pvanroy/Tektronix-CCD-Cooler/Pictures/IMG_20220201_145929.jpg

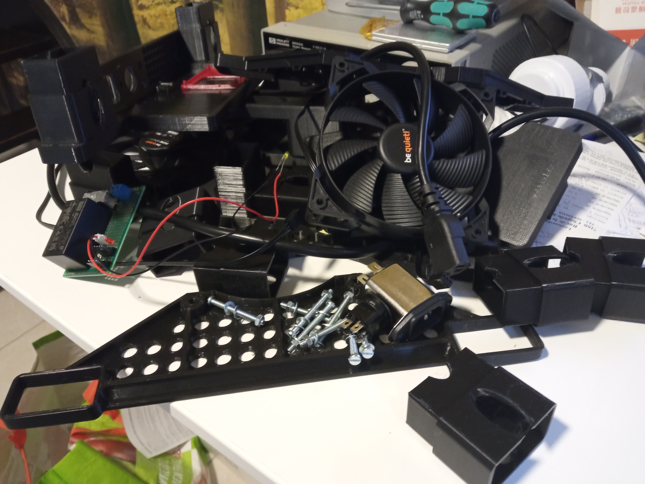
Pictures/IMG_20220201_145929.jpg
