pvanroy/Tektronix-CCD-Cooler/Pictures/IMG_20220201_165314.jpg

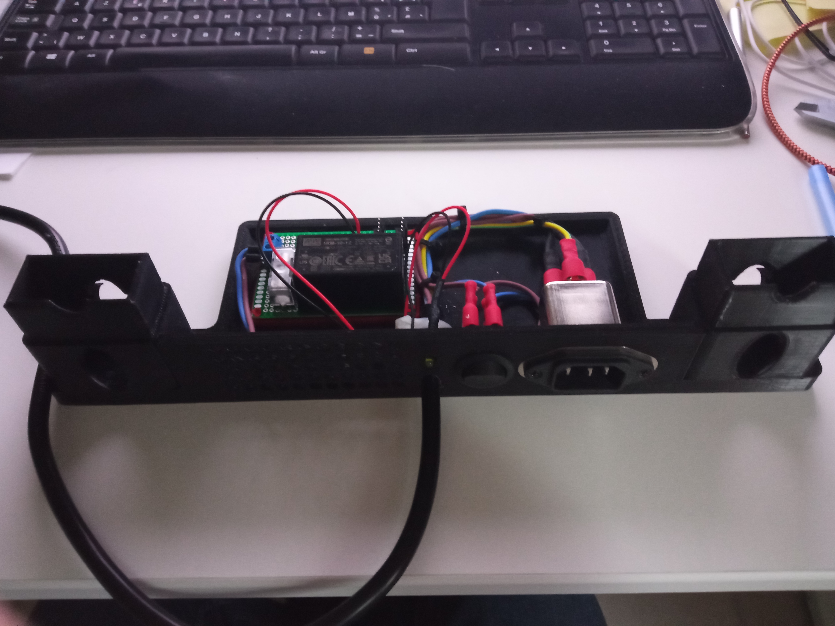
Pictures/IMG_20220201_165314.jpg
