pvanroy/Tektronix-CCD-Cooler/Pictures/IMG_20220201_165510.jpg

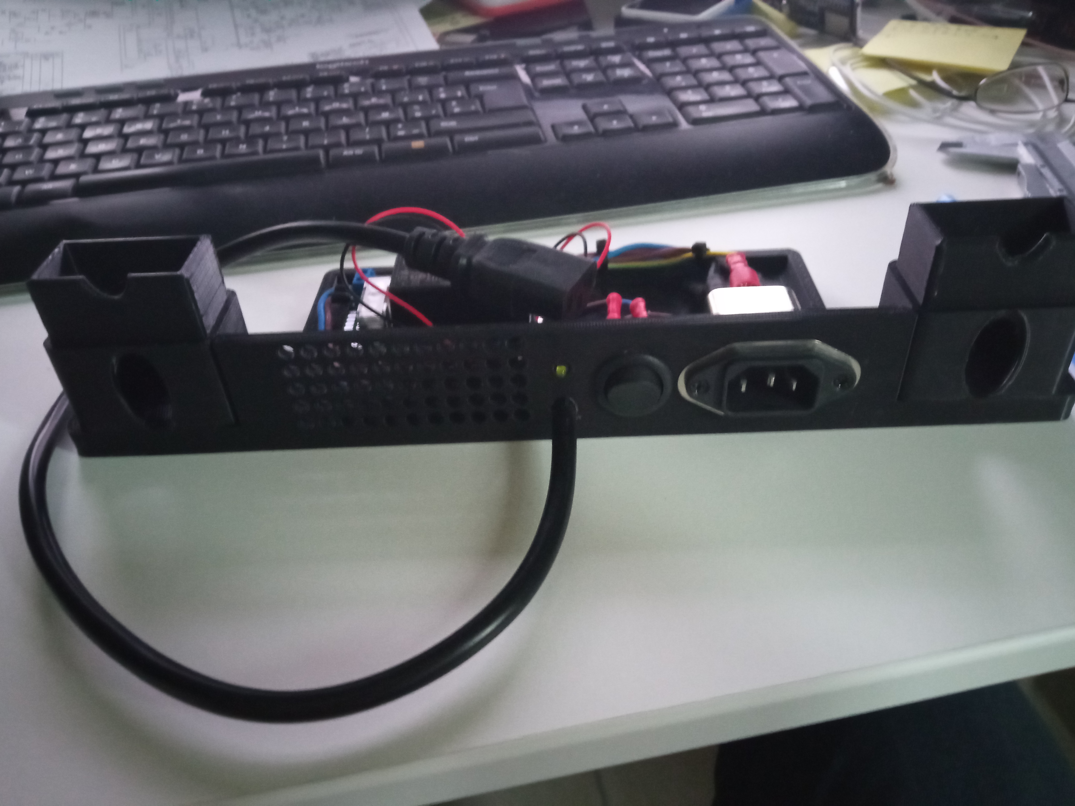
Pictures/IMG_20220201_165510.jpg
