pvanroy/Tektronix-CCD-Cooler/Pictures/IMG_20220201_170256.jpg

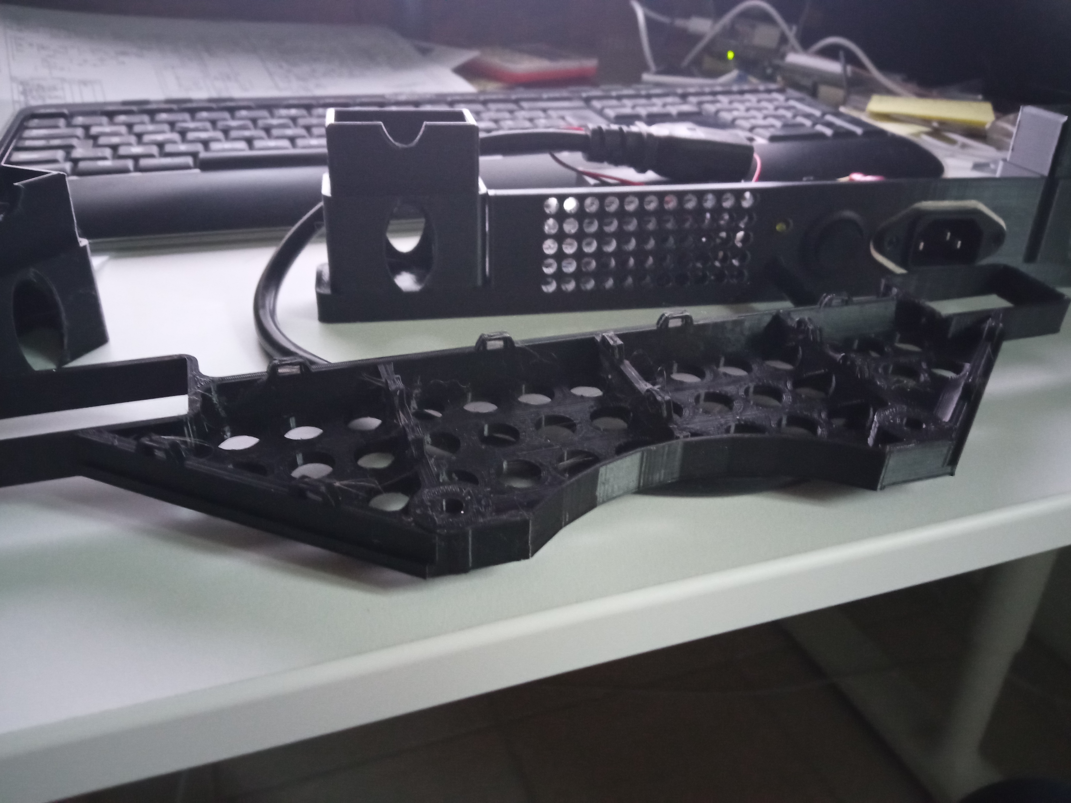
Pictures/IMG_20220201_170256.jpg
