pvanroy/Tektronix-CCD-Cooler/Pictures/IMG_20220201_171011.jpg

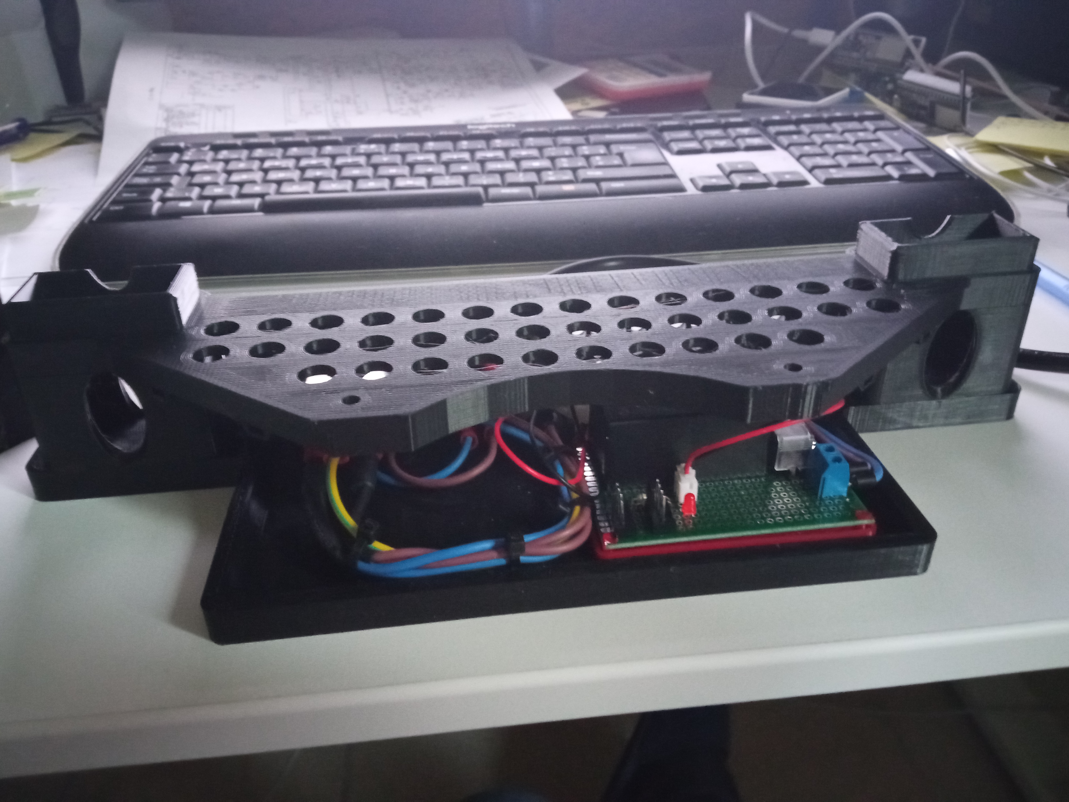
Pictures/IMG_20220201_171011.jpg
