pvanroy/Tektronix-CCD-Cooler/Pictures/IMG_20220201_171432.jpg

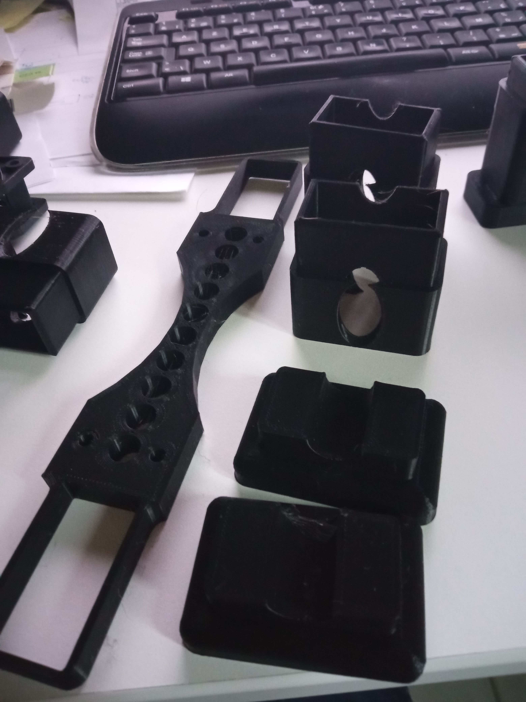
Pictures/IMG_20220201_171432.jpg
