pvanroy/Tektronix-CCD-Cooler/Pictures/IMG_20220202_084107.jpg

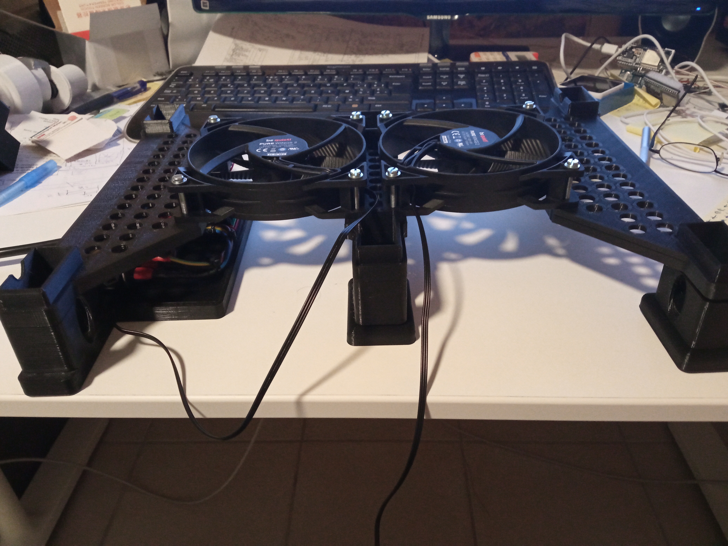
Pictures/IMG_20220202_084107.jpg
