pvanroy/Tektronix-CCD-Cooler/Pictures/IMG_20220202_085803.jpg

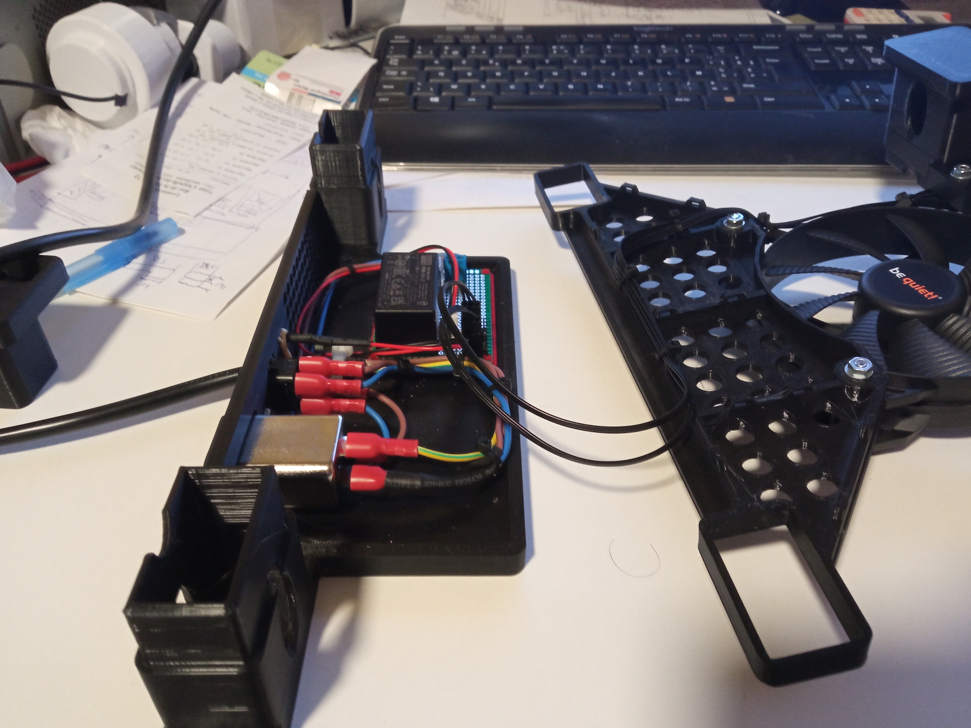
Pictures/IMG_20220202_085803.jpg
