pvanroy/Tektronix-CCD-Cooler/Pictures/IMG_20220202_085853.jpg

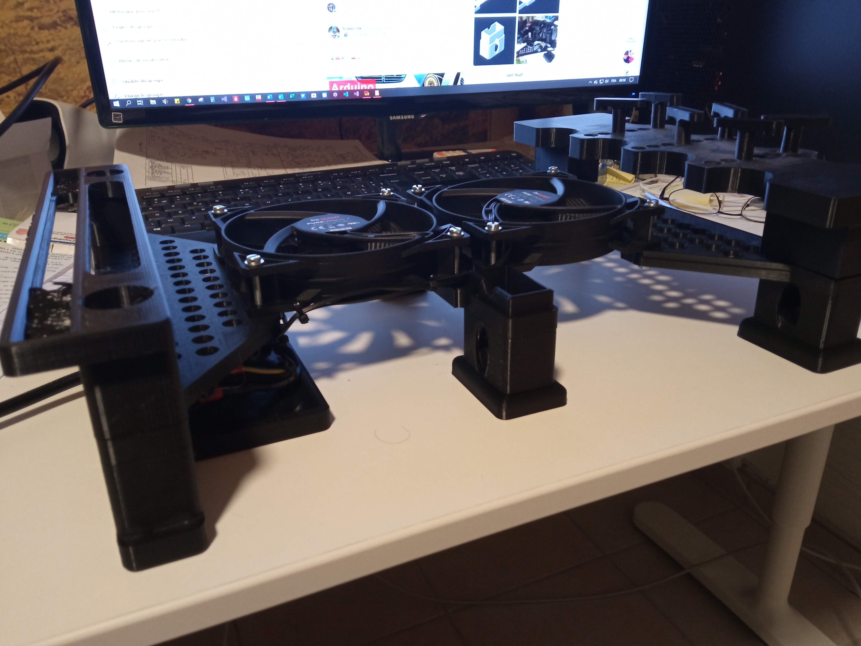
Pictures/IMG_20220202_085853.jpg
