pvanroy/Tektronix-CCD-Cooler/Pictures/IMG_20220202_085902.jpg

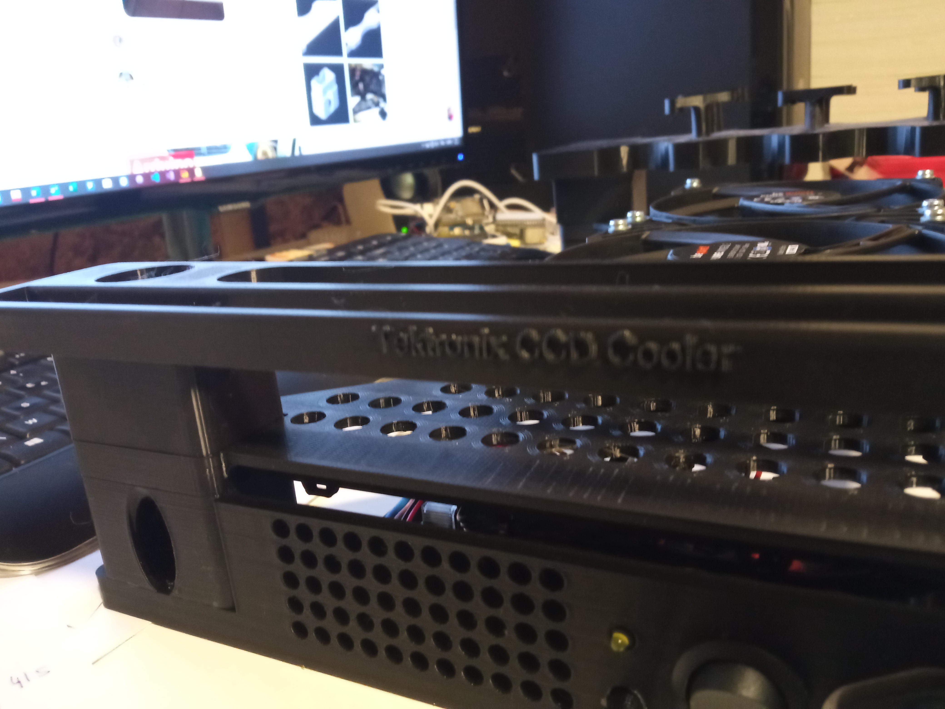
Pictures/IMG_20220202_085902.jpg
