pvanroy/Tektronix-CCD-Cooler/Pictures/IMG_20220202_090543.jpg

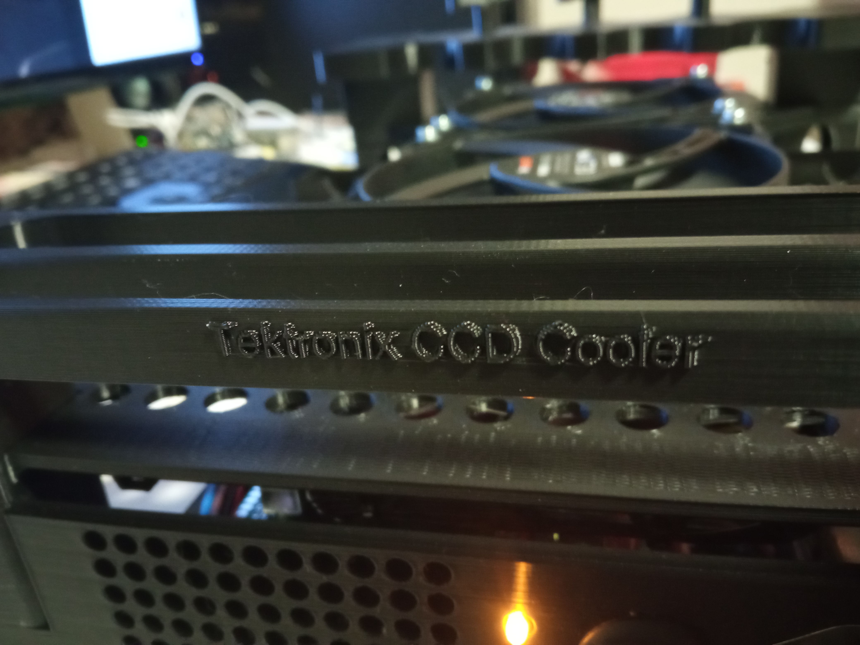
Pictures/IMG_20220202_090543.jpg
