pvanroy/Tektronix-CCD-Cooler/Pictures/IMG_20220208_113421.jpg

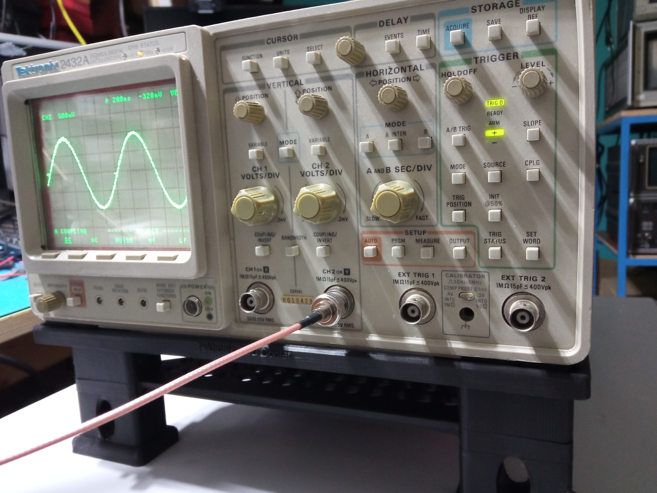
Pictures/IMG_20220208_113421.jpg
