pvanroy/Tektronix-CCD-Cooler/Pictures/IMG_20220208_113443.jpg

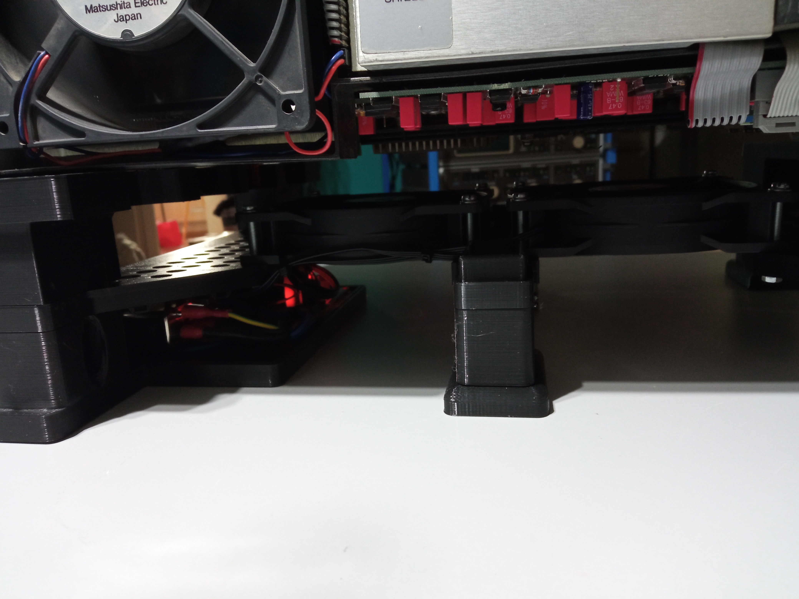
Pictures/IMG_20220208_113443.jpg
