pvanroy/Tektronix-CCD-Cooler/Pictures/IMG_20220208_113453.jpg

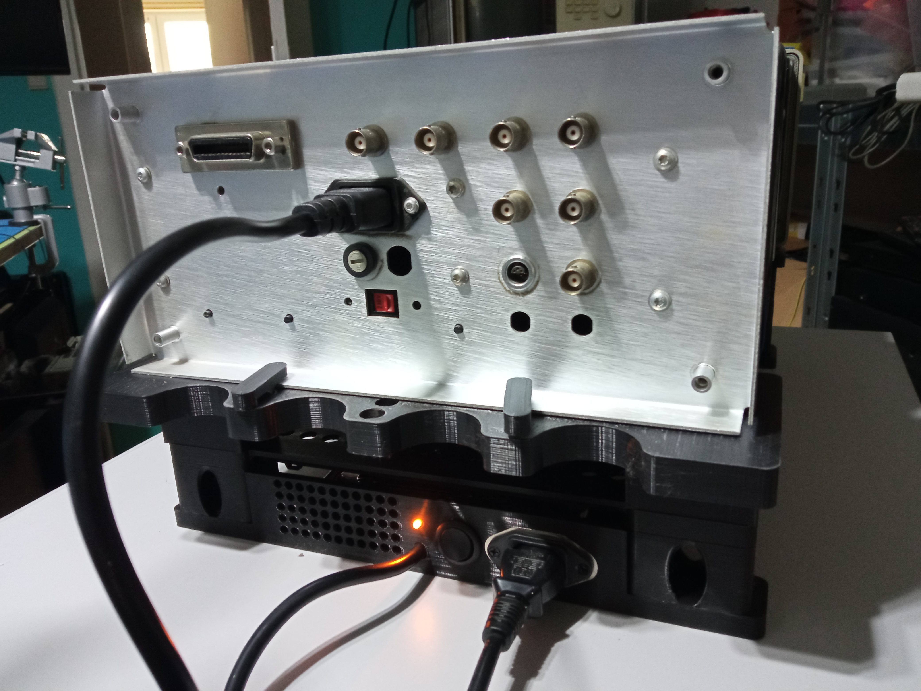
Pictures/IMG_20220208_113453.jpg
