pvanroy/Tektronix-CCD-Cooler/Pictures/IMG_20220208_122140.jpg

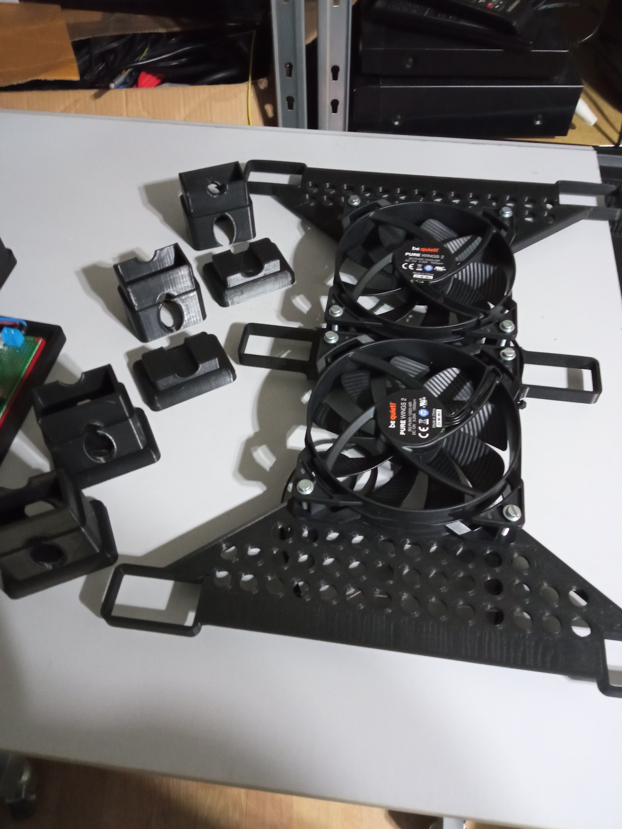
Pictures/IMG_20220208_122140.jpg
