pvanroy/Tektronix-CCD-Cooler/Pictures/IMG_20220208_122149.jpg

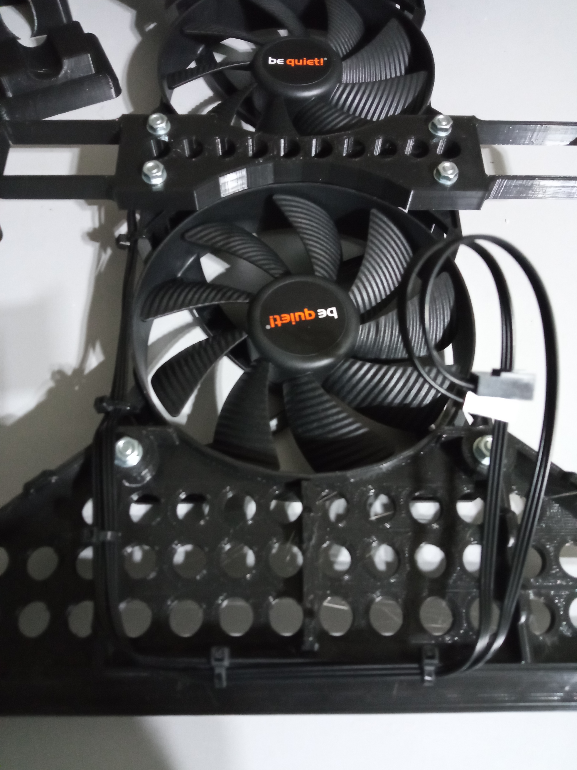
Pictures/IMG_20220208_122149.jpg
