pvanroy/Tektronix-CCD-Cooler/Pictures/IMG_20220208_124335.jpg

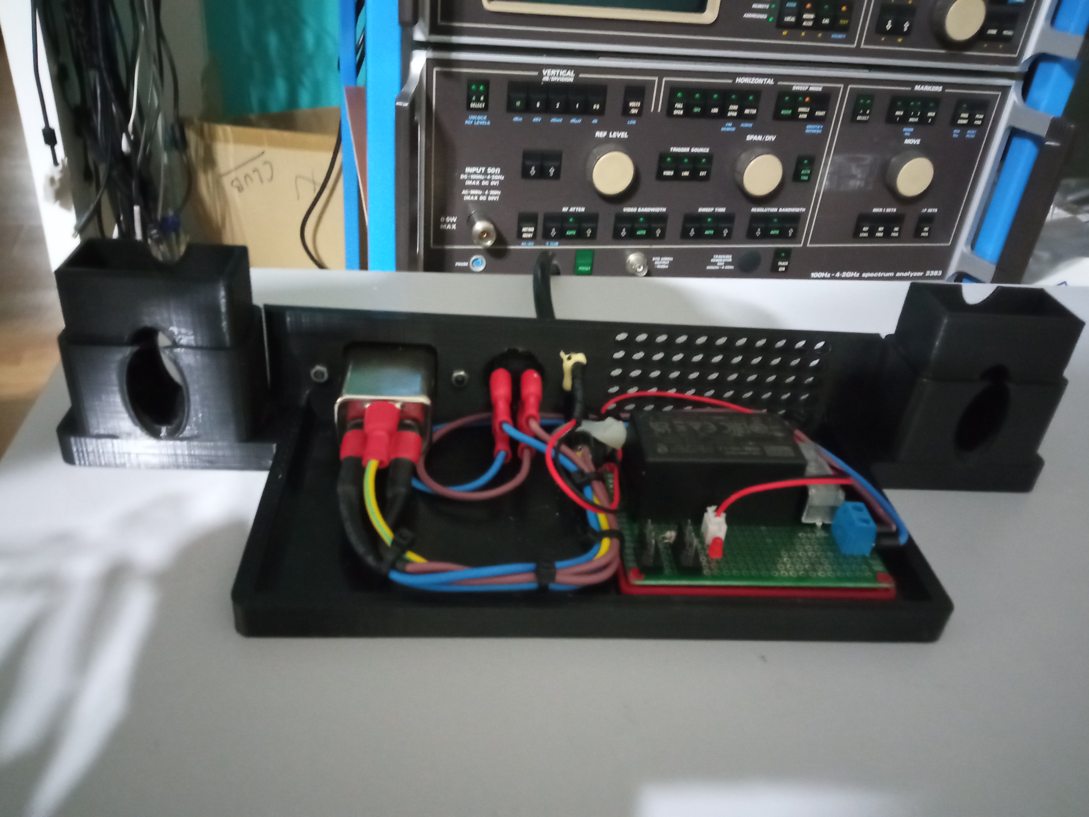
Pictures/IMG_20220208_124335.jpg
