pvanroy/Tektronix-CCD-Cooler/Pictures/IMG_20220208_124656.jpg

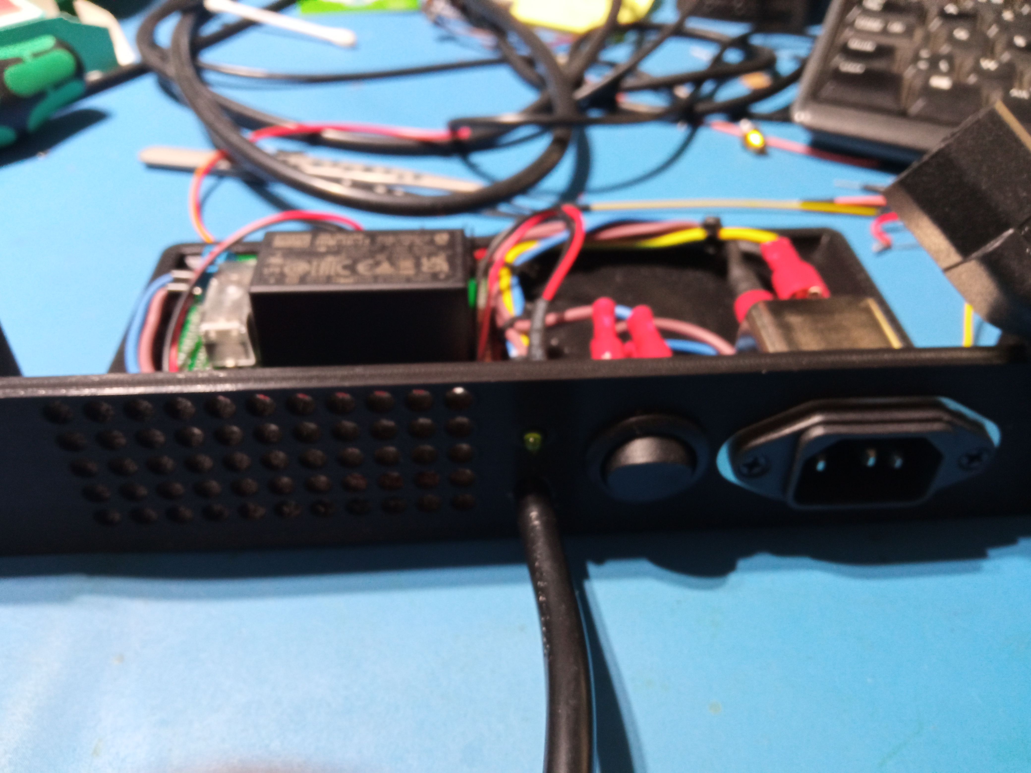
Pictures/IMG_20220208_124656.jpg
