pvanroy/Tektronix-CCD-Cooler/Pictures/IMG_20220208_130855.jpg

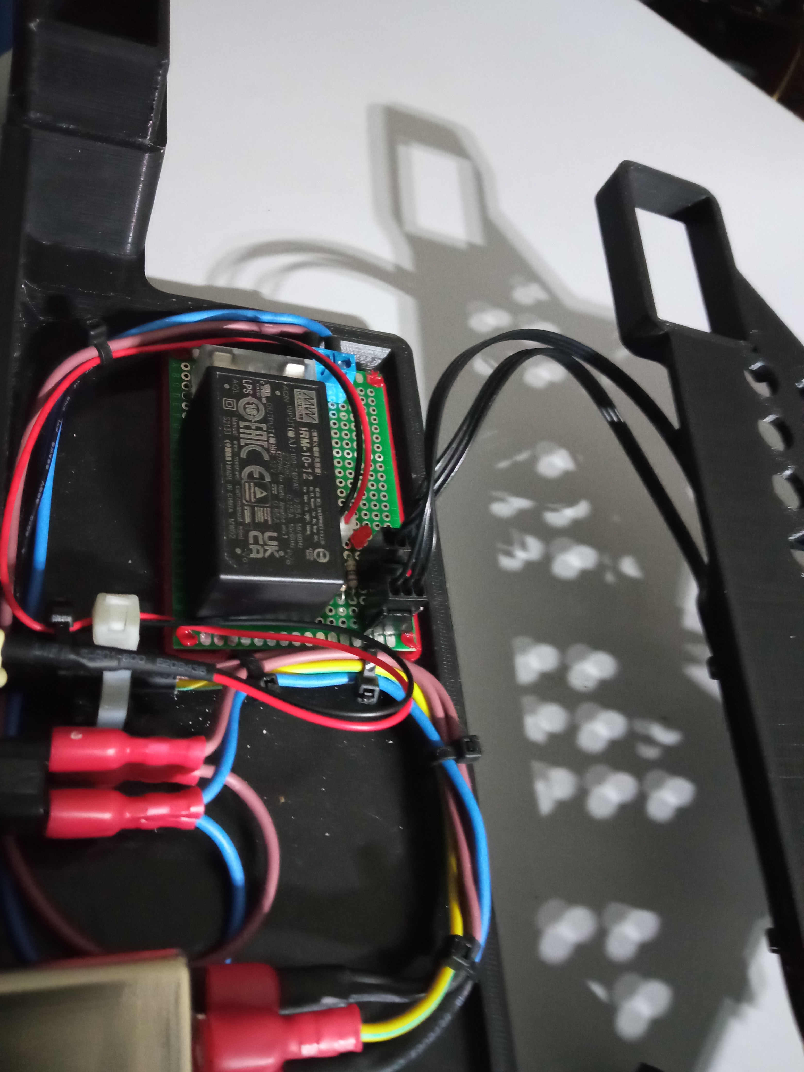
Pictures/IMG_20220208_130855.jpg
