pvanroy/Tektronix-CCD-Cooler/Pictures/IMG_20220208_130916.jpg

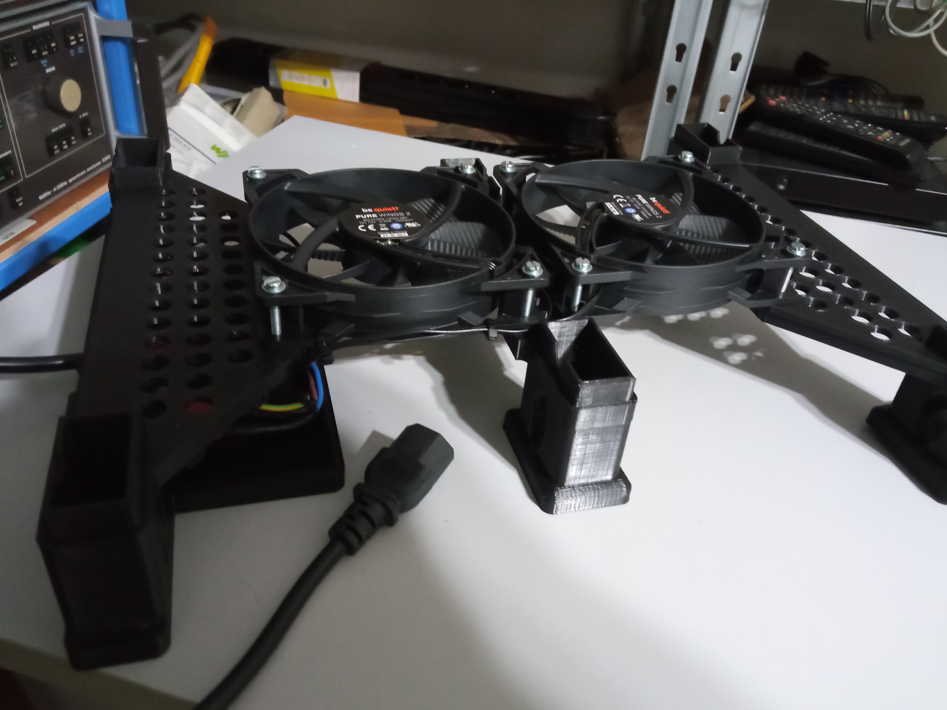
Pictures/IMG_20220208_130916.jpg
