pvanroy/Tektronix-CCD-Cooler/Pictures/IMG_20220208_131827.jpg

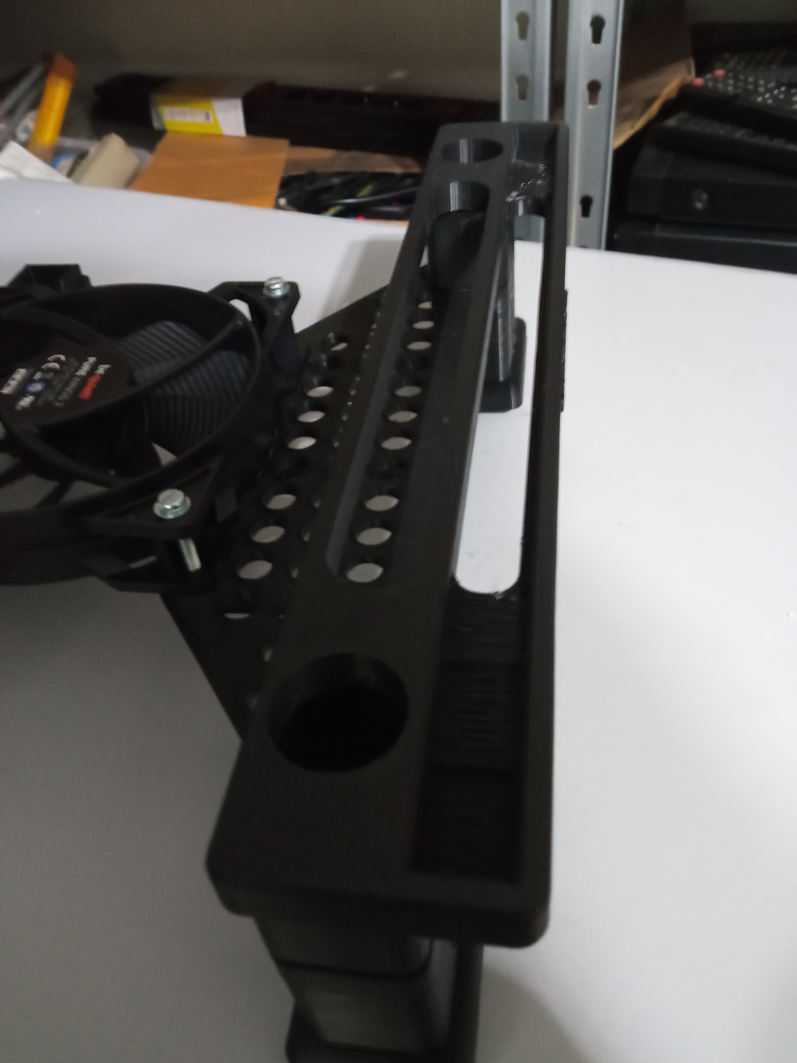
Pictures/IMG_20220208_131827.jpg
