pvanroy/Tektronix-CCD-Cooler/Pictures/Rear_Vent_Plate.JPG

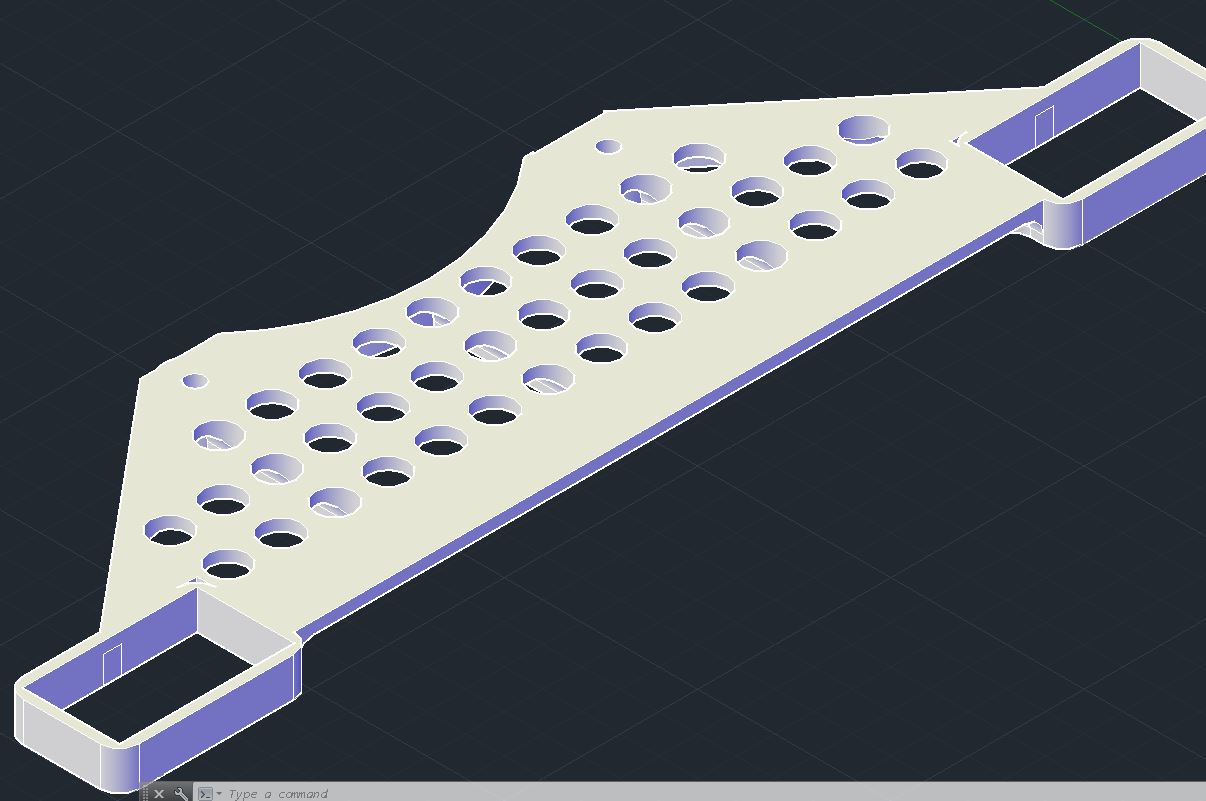
Pictures/Rear_Vent_Plate.JPG
